MZandtheRaspberryPi/magic_box/ecad/schematic_for_box_v13.sch

## EAGLE design ecad/schematic_for_box_v13.sch (2022-03-31)

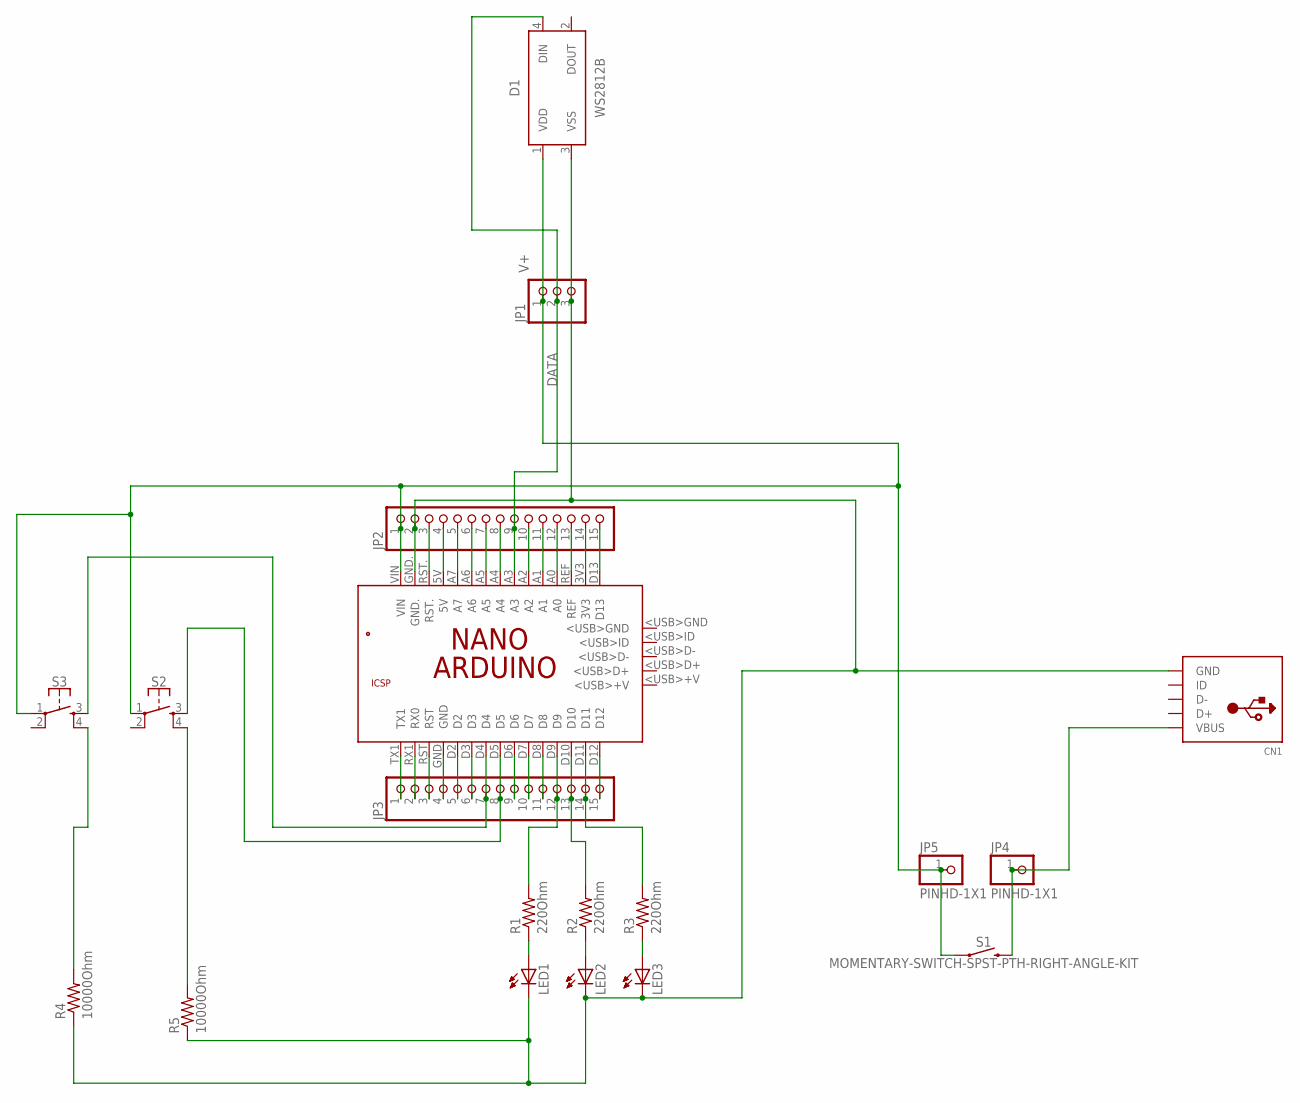
[picture p14: schematic schematic_for_box_v13.sch]

Parts:
CN1: USBMINIB; USB-MINIB
D1: WS2812B
JP1: PINHD-1X3; 1X03
JP2, JP3: PINHD-1X15; 1X15
JP4, JP5: PINHD-1X1; 1X01
LED1, LED2, LED3: LED3MM
PCB1: ARDUINO_NANO
R1, R2, R3: 220Ohm; 0805-THM
R4, R5: 10000Ohm; 0805-THM
S1: MOMENTARY-SWITCH-SPST-PTH-RIGHT-ANGLE-KIT; TACTILE_SWITCH_PTH_RIGHT_ANGLE_KIT
S2, S3: MOMENTARY-SWITCH-SPST-2-SMD-5.2MM; TACTILE_SWITCH_SMD_5.2MM

Connections:
DATA: D1.4 (DIN), JP1.2, JP2.9, PCB1.A3
GND: CN1.GND, D1.3 (VSS), JP1.3, JP2.2, LED1.K (C), LED2.K (C), LED3.K (C), PCB1.GND., R4.1, R5.1
unnamed: CN1.VBUS, JP4.1, S1.2
unnamed: JP3.1, PCB1.TX1
unnamed: JP2.15, PCB1.D13
unnamed: JP2.14, PCB1.3V3
unnamed: JP3.8, PCB1.D5, S2.3
unnamed: JP2.13, PCB1.REF
unnamed: LED1.A, R1.1
unnamed: JP3.7, PCB1.D4, S3.3
unnamed: JP3.2, PCB1.RX1 (RX0)
unnamed: LED2.A, R2.1
unnamed: JP3.12, PCB1.D9, R1.2
unnamed: LED3.A, R3.1
unnamed: R4.2, S3.4
unnamed: R5.2, S2.4
unnamed: JP2.12, PCB1.A0
unnamed: JP2.11, PCB1.A1
unnamed: JP2.10, PCB1.A2
unnamed: JP2.8, PCB1.A4
unnamed: JP2.7, PCB1.A5
unnamed: JP2.6, PCB1.A6
unnamed: JP2.5, PCB1.A7
unnamed: JP2.4, PCB1.5V
unnamed: JP2.3, PCB1.RST.
unnamed: JP3.3, PCB1.RST
unnamed: JP3.4, PCB1.GND
unnamed: JP3.5, PCB1.D2
unnamed: JP3.6, PCB1.D3
unnamed: JP3.10, PCB1.D7
unnamed: JP3.11, PCB1.D8
unnamed: JP3.9, PCB1.D6
unnamed: JP3.13, PCB1.D10, R2.2
unnamed: JP3.14, PCB1.D11, R3.2
unnamed: JP3.15, PCB1.D12
V+: D1.1 (VDD), JP1.1, JP2.1, JP5.1, PCB1.VIN, S1.1, S2.1, S3.1
